ryoo14/keyboards/low-profile/case/low-profile-sidebar.step

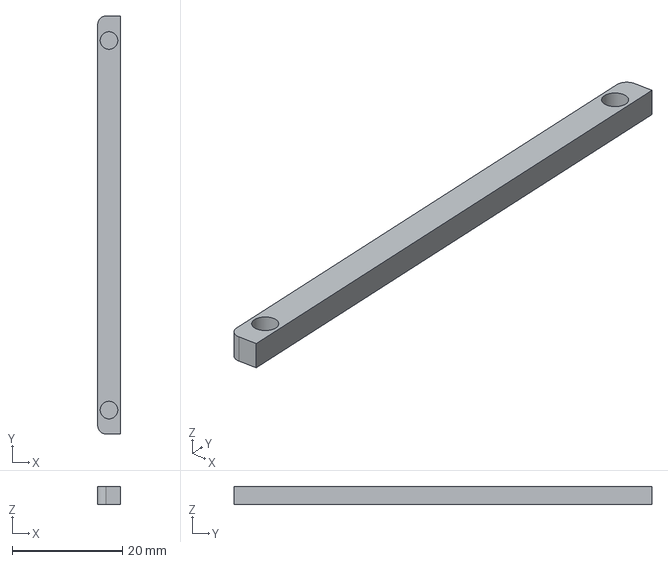
[picture p14: CAD file, 2025-11-08]
low-profile/case/low-profile-sidebar.step
4.10 x 75.9 x 3.30 mm
