ryoo14/keyboards/low-profile/case/rhyl47_pcb.step

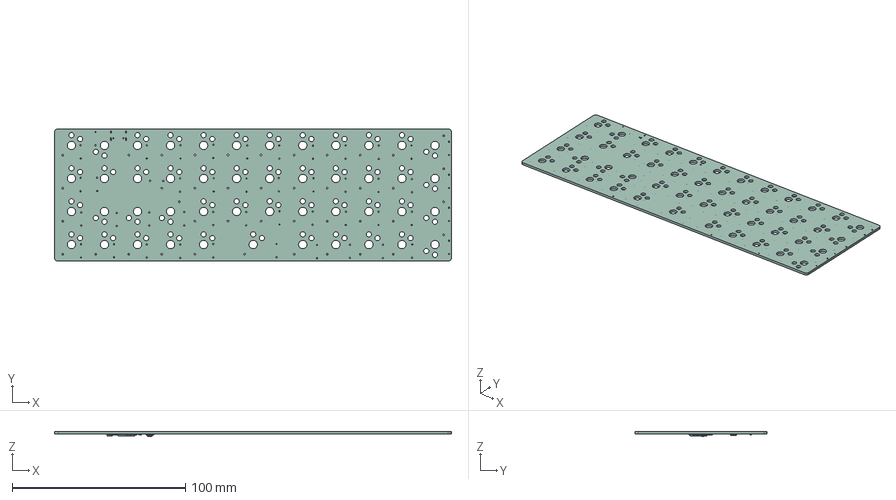
[picture p15: CAD file, 2025-10-01]
low-profile/case/rhyl47_pcb.step
228.8 x 76.2 x 2.79 mm
C_0402_1005Metric x 14
R_0402_1005Metric x 7
QFN-56-1EP_7x7mm_P0.4mm_EP3.2x3.2mm
Fuse_1206_3216Metric
SOT-23-3
Resonator_SMD_Murata_CSTxExxV-3Pin_3.0x1.1mm
rhyl47_pcb_PCB
